pavelkozh/sorting-graduate_work/blueprints/Держатель1.SLDPRT

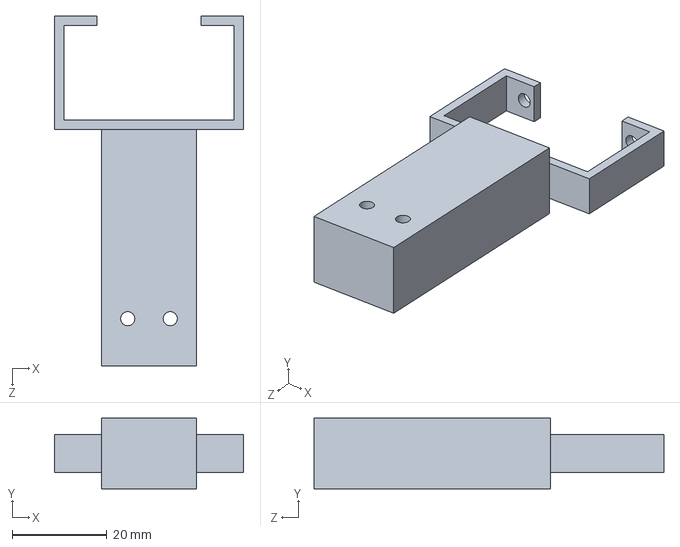
[picture p15: CAD file, 2021-03-10]
blueprints/Держатель1.SLDPRT
40.0 x 15.0 x 74.0 mm
