pavelkozh/sorting-graduate_work/blueprints/Труба.SLDPRT

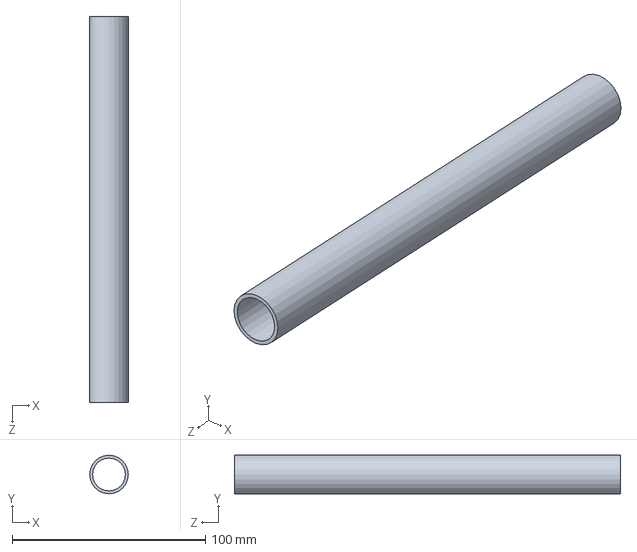
[picture p16: CAD file, 2021-03-08]
blueprints/Труба.SLDPRT
20.0 x 20.0 x 200.0 mm
