pavelkozh/sorting-graduate_work/blueprints/Желоб.SLDPRT

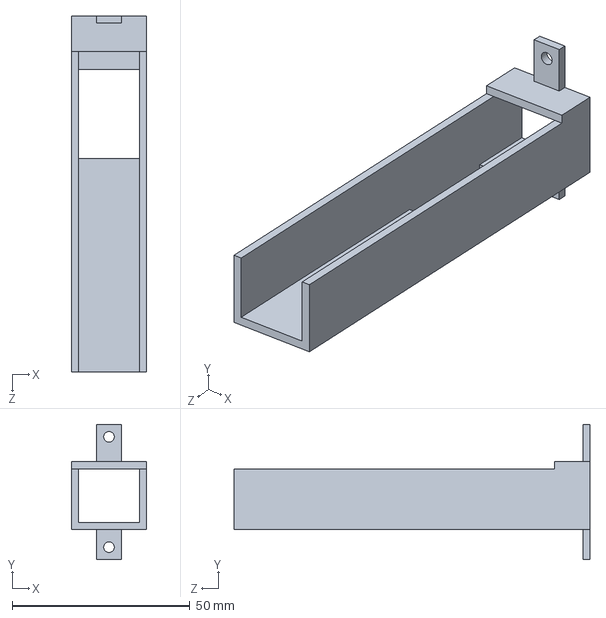
[picture p17: CAD file, 2021-03-05]
blueprints/Желоб.SLDPRT
21.0 x 38.0 x 100.0 mm
