pavelkozh/sorting-graduate_work/blueprints/Шестерня.SLDPRT

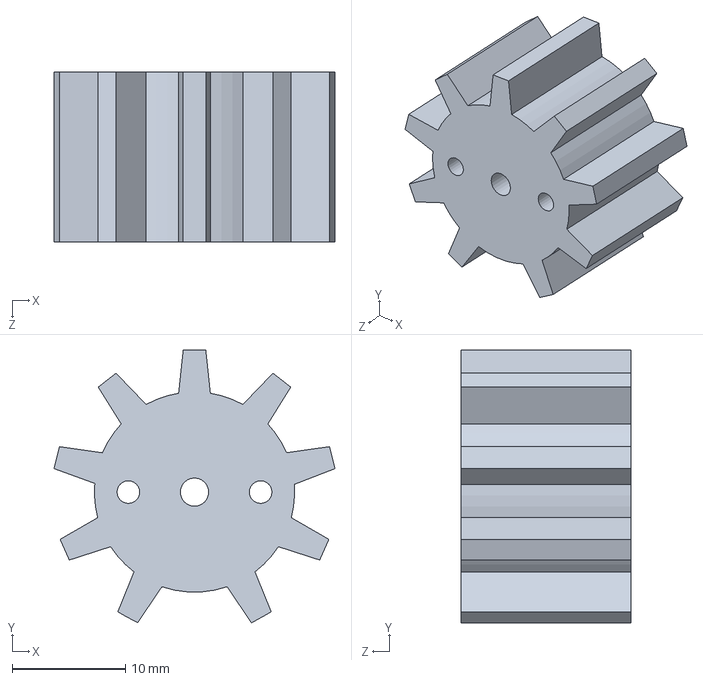
[picture p18: CAD file, 2021-02-23]
blueprints/Шестерня.SLDPRT
24.8 x 24.1 x 15.0 mm
