pavelkozh/sorting-graduate_work/blueprints/Рейка_stl.STL

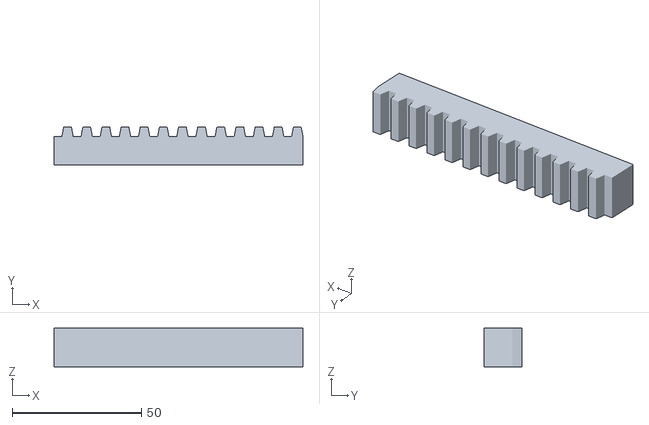
[picture p19: CAD file, 2021-02-21]
blueprints/Рейка_stl.STL
96.2 x 14.7 x 15.0
